SamuelHudec/pg-meteo/docs/1.jpeg

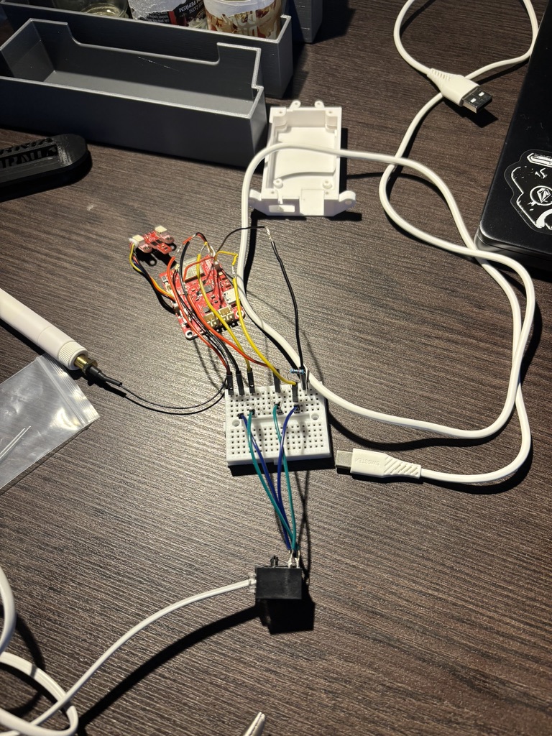
docs/1.jpeg
