SamuelHudec/pg-meteo/docs/2.jpeg

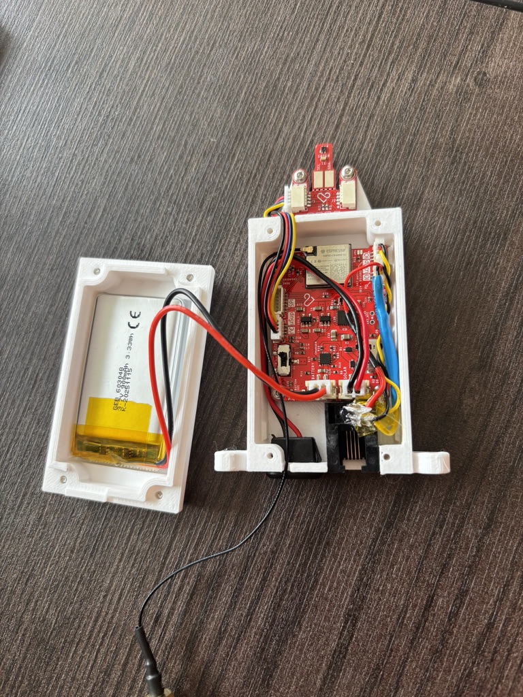
docs/2.jpeg
