SamuelHudec/pg-meteo/docs/3.jpeg

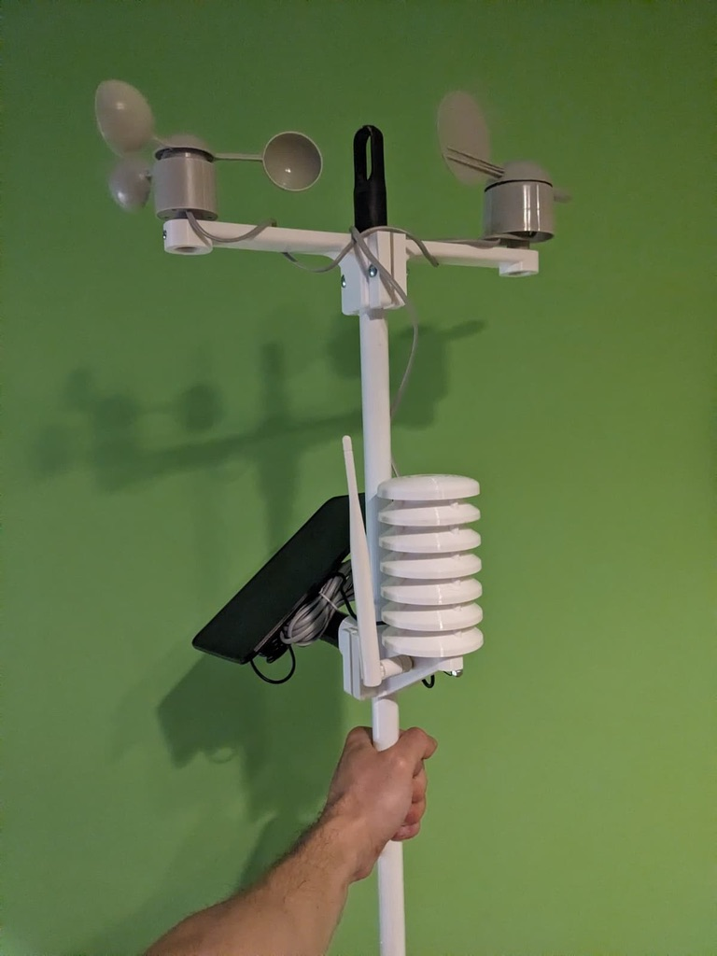
docs/3.jpeg
